SamudraUduwaka/Analog-Lead-Acid-Battery-Charger/final_simulation_x.asc

C1: cap; 2200µ
C2: cap; 100µ
C3: cap; 100µ
C4: cap; 100µ
C5: cap; 100µ
C6: cap; 100µ
D1: zener
D2: zener
D3: LED
D4: LED
D8: zener
D9: zener
L1: ind; 1m
M1: nmos; IRFH5406
Q1: npn
Q2: npn
Q3: npn
Q4: npn
Q5: npn
R1: res; 1K
R3: res; 10K
R4: res; 10K
R5: res; 10k
R6: res; 10.1k
R7: res; 330k
R8: res; 330k
R9: res; 11k
R10: res; 3K
R11: res; 15K
R12: res; 100
R13: res; 17K
R14: res; 5k
R15: res; 1k
R16: res; 10K
R17: res; 100K
R18: res; 100K
R19: res; 100K
R20: res; 1K
R21: res; 100K
R24: res; 100
R25: res; 0.22
R26: res; 120k
R27: res; 150k
U1: UniversalOpAmp2
U2: UniversalOpAmp2
U3: UniversalOpAmp2
U4: UniversalOpAmp2
U6: UniversalOpAmp2
V1: voltage; 9
V2: voltage; 9
V3: voltage; 15
V4: voltage; 15
V5: voltage; 15
V6: voltage; 5
V7: voltage; 15
V8: voltage; 15
V9: voltage; 15
V10: voltage; 15
V11: battery; PULSE(5.6 13.3 0 150m 0 150m 300m 1); Rser=0.5
V15: voltage; 15
V16: voltage; 20
V17: voltage; PULSE(5 10 0 2.25u 2.25u 0 4.5u)
Named nets: 0
CONTROL VOLTAGE
CONTROL CURRENT
Battery voltage
c1
c2
BATTERY VOLTAGE
CONSTANT CURRENT
20V
PWM
battery voltage
buck converter
.tran 300m
comparator
high
constant voltage
CONSTANT CURRENT
CONSTANT VOLTAGE
COMPARATOR
;tran 250m
potentiometer
potentiometer
potentiometer
potentiometer
